MoSetlo/Thesis2024/Simulations/PushPullInductaneCombo.asc

D1: schottky; RBR3MM40B
D2: schottky; RBR3MM40B
D3: schottky; RBR3MM40B
D4: schottky; RBR3MM40B
L1: ind; 100µ
L2: ind; 100µ
L3: ind; 100µ
L4: ind; 100µ
M1: nmos; PMV45EN2
M2: nmos; PMV45EN2
M3: nmos; PMV45EN2
M4: nmos; PMV45EN2
Q1: npn; 2N2222
Q2: pnp; 2N2907
Q3: npn; 2N2222
Q4: pnp; 2N2907
Q5: npn; 2N2222
Q6: pnp; 2N2907
Q7: npn; 2N2222
Q8: pnp; 2N2907
R1: res; 18
R2: res; 10
R3: res; 1.2
R4: res; 10
R5: res; 1.2
R6: res; 18
R7: res; 10
R8: res; 1.2
R9: res; 18
R10: res; 10
R11: res; 1.2
R12: res; 18
V1: voltage; PULSE(0 3.3 0 50n 50n 1.25u 25u 10)
V2: voltage; 3.7
V3: voltage; 0.2
V4: voltage; 0.2
V5: voltage; 0.2
V6: voltage; 0.2
V7: voltage; PULSE(3.3 0 0 50n 50n 1.25u 25u 10)
Named nets: 0
.tran 0 100u 0 25u
.inc PMV45EN2_26_5_2014.lib
